aidanjgriffiths/Project-Plant/hardware/documentation/Design 01 - Spaghetti.jpg

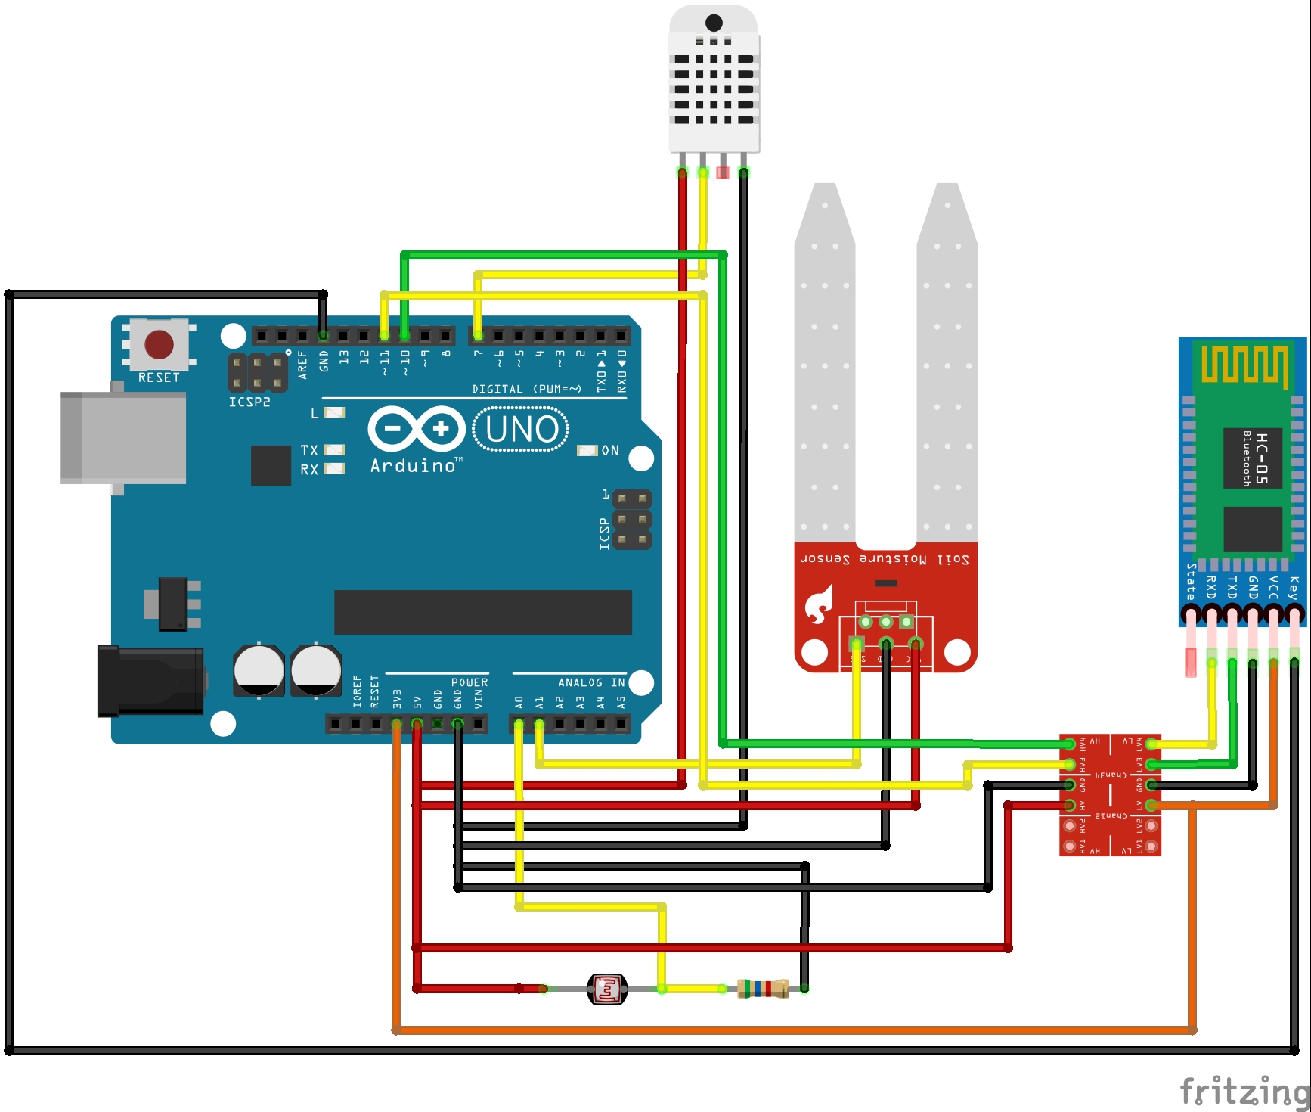
hardware/documentation/Design 01 - Spaghetti.jpg
