aidanjgriffiths/Project-Plant/hardware/Schematic/Schematic_Spagetti.png

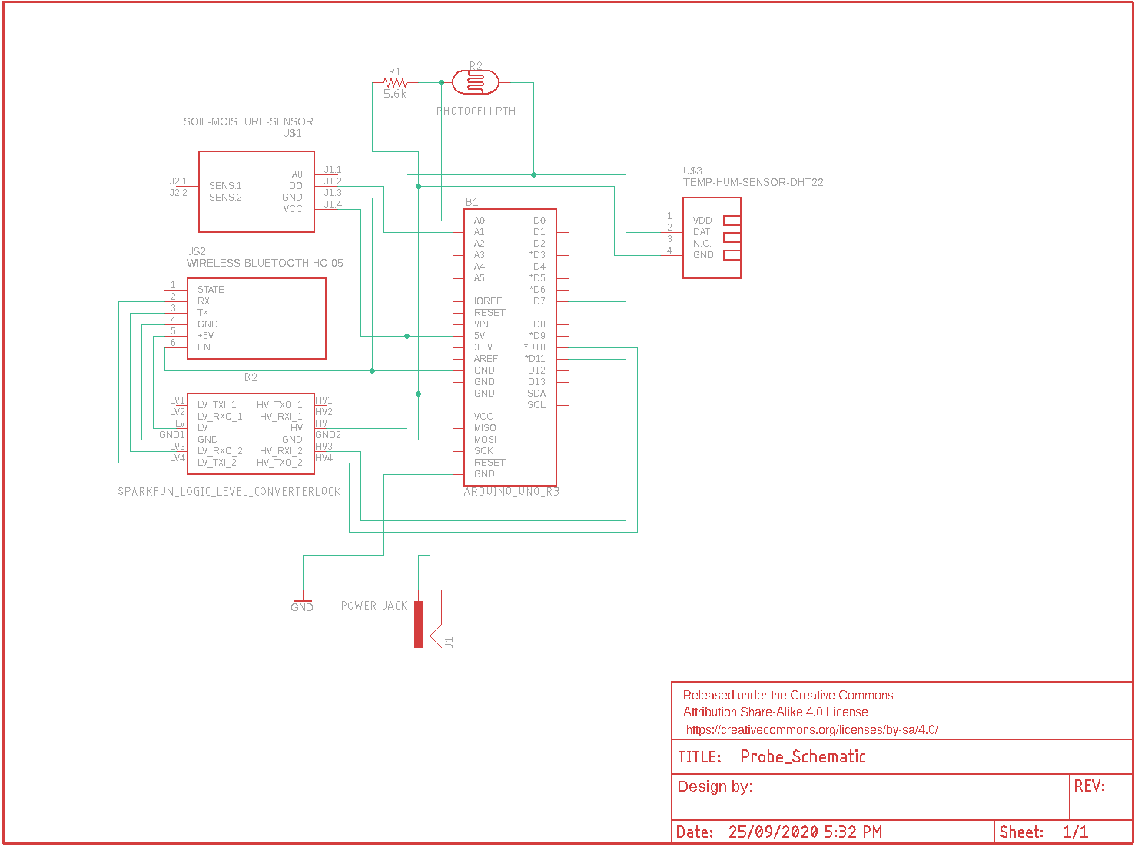
hardware/Schematic/Schematic_Spagetti.png
