aidanjgriffiths/Project-Plant/PlantifulWeb/Documentation/Infrastructure.png

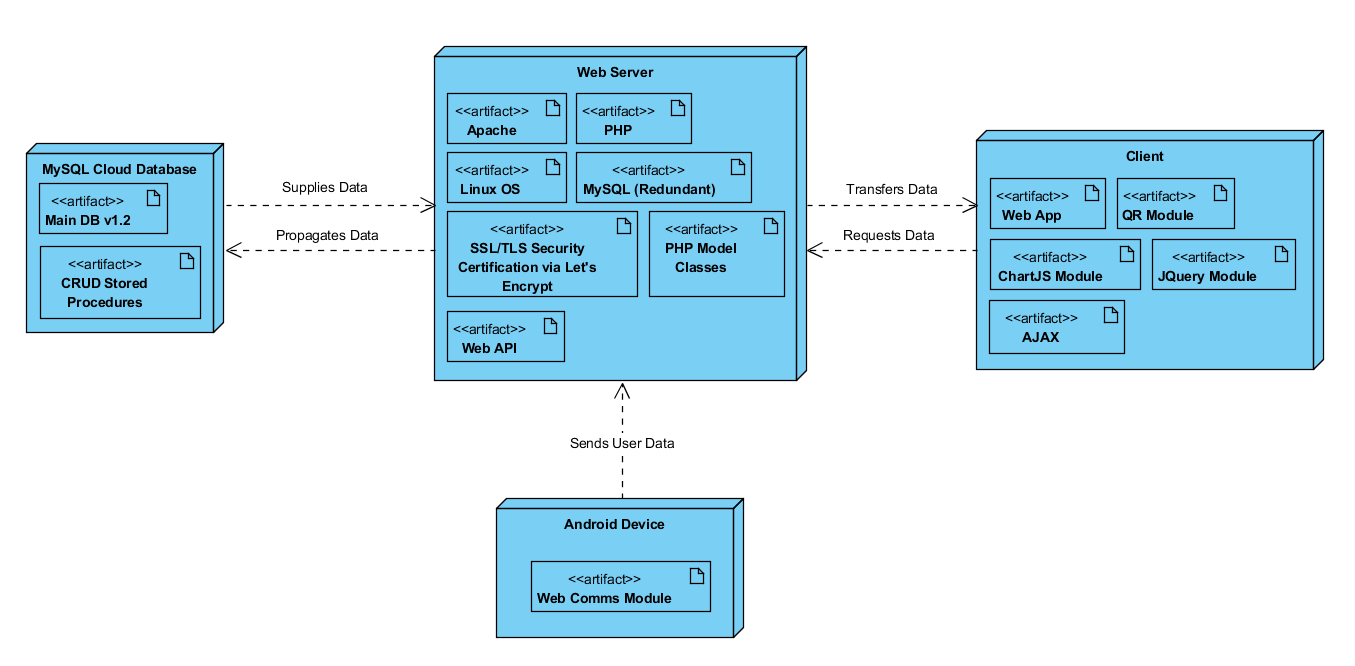
PlantifulWeb/Documentation/Infrastructure.png
