aidanjgriffiths/Project-Plant/hardware/documentation/Testers.jpg

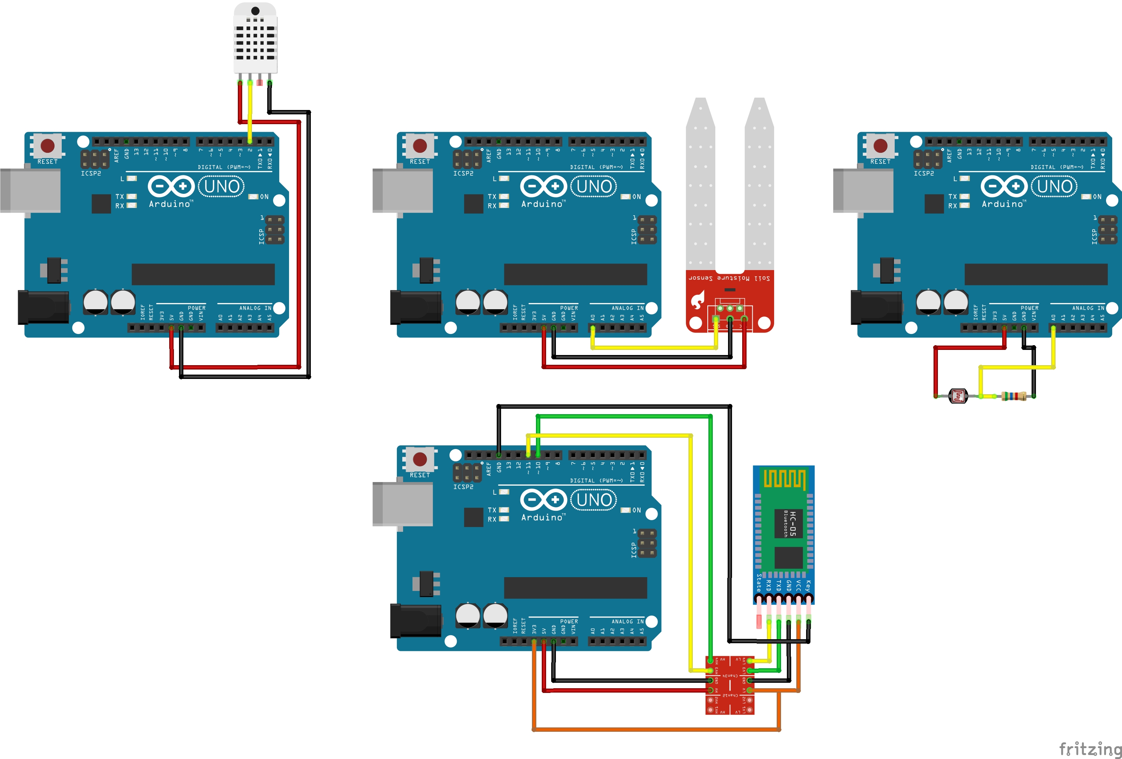
hardware/documentation/Testers.jpg
