aidanjgriffiths/Project-Plant/hardware/Simulator/Simulator.ino

#include <SoftwareSerial.h>
#define VERSION "SIM0.2"
#define BLUETOOTH_RX 11
#define BLUETOOTH_TX 10
#define BLUETOOTH_BAUD 9600

char buf[30];
int temp = 25;
int humidity = 65;
int light = 50;
int moisture = 50;

SoftwareSerial bluetooth(BLUETOOTH_RX, BLUETOOTH_TX);

void setup()
{
  bluetooth.begin(BLUETOOTH_BAUD);
}

void adjustValues()
{
  int adjustTemp = random(0,100);
  int adjustHumidity = random(0,100);
  int adjustLight = random(0, 100);
  int adjustMoisture = random(0, 100);

  adjustValue(temp, adjustTemp, 15, 35);
  adjustValue(humidity, adjustHumidity, 20, 80);
  adjustValue(light, adjustLight, 100, 5000);
  adjustValue(moisture, adjustMoisture, 20, 80);
}

void adjustValue(int &adjustVariable, int &adjustPressure, int minimum, int maximum)
{
  if (adjustPressure < 33 && adjustVariable > minimum)
  {
    adjustVariable = adjustVariable - 2;
  }
  else if (adjustPressure > 66 && adjustVariable < maximum)
  {
    adjustVariable = adjustVariable + 2;
  }
}

void loop()
{
  if (bluetooth.available())
  {
    char c = bluetooth.read();
    c = tolower(c);

    switch(c)
    {
      case 'v':
        strcpy(buf, VERSION);
        strcat(buf, "\r\n");
        bluetooth.print(buf);
        break;
      case 'r':
        char numbers[5];
        
        adjustValues();

        strcpy(buf, "T");
        strcat(buf, itoa(temp, numbers, 10));
        strcat(buf, "H");
        strcat(buf, itoa(humidity, numbers, 10));
        strcat(buf, "L");
        strcat(buf, itoa(light, numbers, 10));
        strcat(buf, "M");
        strcat(buf, itoa(moisture, numbers, 10));
        bluetooth.println(buf);
        break;
    }
  }
}
